miko53/zigbee_temp_sensor/firmware/timer.h

/*
 * File:   timer.h
 * Author: mickael
 *
 * Created on 15 août 2016, 18:29
 */

#ifndef TIMER_H
#define	TIMER_H

#ifdef	__cplusplus
extern "C" {
#endif

extern void timer0_wait_65ms(void);
extern void timer0_wait_262ms(void);


#ifdef	__cplusplus
}
#endif

#endif	/* TIMER_H */
