miko53/zigbee_temp_sensor/firmware/timer_loc.h

/*
 * File:   timer_loc.h
 * Author: mickael
 *
 * Created on 15 août 2016, 18:29
 */

#ifndef TIMER_LOC_H
#define	TIMER_LOC_H

#ifdef	__cplusplus
extern "C" {
#endif

#include <xc.h>

extern BOOL timer0_interupt_done;

#ifdef	__cplusplus
}
#endif

#endif	/* TIMER_LOC_H */
