miko53/zigbee_temp_sensor/firmware/osc.h

/*
 * File:   osc.h
 * Author: mickael
 *
 * Created on 15 novembre 2015, 16:26
 */

#ifndef OSC_H
#define	OSC_H

#include <stdint.h>

extern volatile int8_t calibr;
extern void calibration(void);


#endif	/* OSC_H */
